mbouyer/marine_chartplotter/software/edisplay/pic/usb.c

// Firmware framework for USB I/O on PIC 18F2455 (and siblings)
// Copyright (C) 2005 Alexander Enzmann
//
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
// Modifications for SDCC2.8.0 and for loading under UBW Bootloader

#include <pic18fregs.h>
#include <string.h>
#include <stdio.h>
#include "usb.h"
#include "version.h"

#define ALLOW_SUSPEND 0

// DBUG_LEVL bitmasks to turn on/off verbosity 
// Excessive debug use may cause USB Congestion .. YMMV 
#define DBUG_CALL 9
#define DBUG_PTXN 8
#define DBUG_UTXN 7
#define DBUG_UDAT 6	
#define DBUG_UCFG 5	
#define DBUG_UGEN 4	
#define DBUG_UVENDOR 3	
#define DBUG_UNU1 2	
#define DBUG_UNU0 1	
#
// DBUG_LEVL >= 0x 80:Calls 40:ProcUSBTxns 20:Data 10:Config 08:Generic 04:VENDOR
// eg For debug messages for all below "ProcessUSBTransactions()"	
//#define DBUG_LEVL 0x3F
#define DBUG_LEVL 0x00

// Device and configuration descriptors.	These are used as the
// host enumerates the device and discovers what class of device
// it is and what interfaces it supports.
#define DEVICE_DESCRIPTOR_SIZE 0x12
#define CONFIG_HEADER_SIZE	0x09
#define VENDOR_DESCRIPTOR_SIZE 0x20
#define VENDOR_HEADER_SIZE 0x09 
typedef struct _configStruct {
	byte configHeader[CONFIG_HEADER_SIZE];
	byte VENDORDescriptor[VENDOR_DESCRIPTOR_SIZE];
} ConfigStruct;

// Global variables
byte deviceState;
byte remoteWakeup;
byte deviceAddress;
byte selfPowered;
byte currentConfiguration;

// Control Transfer Stages - see USB spec chapter 5
#define SETUP_STAGE		0 // Start of a control transfer (followed by 0 or more data stages)
#define DATA_OUT_STAGE 1 // Data from host to device
#define DATA_IN_STAGE	2 // Data from device to host
#define STATUS_STAGE	 3 // Unused - if data I/O went ok, then back to Setup

byte ctrlTransferStage; // Holds the current stage in a control transfer
byte VENDORPostProcess;	// Set to 1 if VENDOR needs to process after the data stage
byte requestHandled;	// Set to 1 if request was understood and processed.

byte *outPtr;		// Data to send to the host
byte *inPtr;		// Data from the host
word wCount;		// Number of bytes of data

// VENDOR Class variables
byte VENDORIdleRate;
byte VENDORProtocol;	// [0] Boot Protocol [1] Report Protocol
byte VENDORRxLen;	// # of bytes put into buffer

const byte deviceDescriptor[] =
{
	0x12, 0x01, // bLength, bDescriptorType
	0x00, 0x02, // bcdUSB (low byte), bcdUSB (high byte)
	0xff, 0xff, // bDeviceClass, bDeviceSubClass
	0xff, E0SZ, // bDeviceProtocl, bMaxPacketSize
	0xD8, 0x04, // idVendor (low byte), idVendor (high byte)
	0x41, 0x45, // idProduct (low byte), idProduct (high byte)
	REV_MINOR, REV_MAJOR, // bcdDevice (low byte), bcdDevice (high byte)
	0x01, 0x02, // iManufacturer, iProduct
	0x00, 0x01  // iSerialNumber (none), bNumConfigurations
};

// Total config size is 0x09 + 0x09 + 0x09 + 0x07 + 0x07+ 0x07 = 0x30
#define CFSZ 0x30

const ConfigStruct configDescriptor =
{
	{
		// Configuration descriptor
		0x09, 0x02, // bLength, bDescriptorType (Configuration)
		CFSZ, 0x00, // wTotalLength (low), wTotalLength (high)
		0x01, 0x01, // bNumInterfaces, bConfigurationValue
		0x00, 0xA0, // iConfiguration, bmAttributes ()
		0x32,	 // bMaxPower
	},
	{
		// VENDOR Interface descriptor
		0x09, 0x04, // bLength, bDescriptorType (Interface)
		0x00, 0x00, // bInterfaceNumber, bAlternateSetting
		0x03, 0xff, // bNumEndpoints, bInterfaceClass (VENDOR)
		0xff, 0xff, // bInterfaceSubclass, bInterfaceProtocol,
		0x00,	 // iInterface
		// VENDOR Endpoint 1 In
		0x07, 0x05, // bLength, bDescriptorType (Endpoint)
		0x81, 0x03, // bEndpointAddress, bmAttributes (Interrupt)
		VENDOR_INPUT_INTR_BYTES, 0x00, // wMaxPacketSize (low), wMaxPacketSize (high)
		0x0a,	 // bInterval (10 millisecond)
		// VENDOR Endpoint 1 Out
		0x07, 0x05, // bLength, bDescriptorType (Endpoint)
		0x01, 0x03, // bEndpointAddress, bmAttributes (Interrupt)
		VENDOR_OUTPUT_INTR_BYTES, 0x00, // wMaxPacketSize (low), wMaxPacketSize (high)
		0x01,	 // bInterval (1 millisecond)
		// VENDOR Endpoint 2 Out
		0x07, 0x05, // bLength, bDescriptorType (Endpoint)
		0x02, 0x02, // bEndpointAddress, bmAttributes (Interrupt)
		VENDOR_OUTPUT_BULK_BYTES, 0x00, // wMaxPacketSize (low), wMaxPacketSize (high)
		0x01,	 // bInterval (1 millisecond)
	}
};

const byte stringDescriptor0[] =
{
	0x04, STRING_DESCRIPTOR,
	0x09, 0x04,
};

const byte stringDescriptor1[] =
{
	0x16, STRING_DESCRIPTOR, // bLength, bDscType
	'M', 0x00, 'B', 0x00, ' ', 0x00, 'd', 0x00,
	'e', 0x00, 'v', 0x00, 'i', 0x00, 'c', 0x00,
	'e', 0x00, 's', 0x00,
};
const byte stringDescriptor2[] =
{
	0x1a, STRING_DESCRIPTOR,
	'U', 0x00, 'S', 0x00, 'B', 0x00, ' ', 0x00,
	'e', 0x00, 'D', 0x00, 'i', 0x00, 's', 0x00,
	'p', 0x00, 'l', 0x00, 'a', 0x00, 'y', 0x00,
};

volatile BDT __at(BDT_BASE + 0x00) ep0Bo;					//Endpoint #0 BD Out
volatile BDT __at(BDT_BASE + 0x04) ep0Bi;					//Endpoint #0 BD In
volatile BDT __at(BDT_BASE + 0x08) ep1Bo;					//Endpoint #1 BD Out
volatile BDT __at(BDT_BASE + 0x0c) ep1Bi;					//Endpoint #1 BD In
volatile BDT __at(BDT_BASE + 0x10) ep2Bo;					//Endpoint #2 BD Out

// TBD: add definitions for additional endpoints (2-16).

// Put endpoint 0 buffers into dual port RAM
#pragma udata usbram4 SetupPacket controlTransferBuffer
volatile setupPacketStruct SetupPacket;
volatile byte controlTransferBuffer[E0SZ];

// Put USB I/O buffers into dual port RAM.
#pragma udata usbram5 VENDORRxBufferB0 VENDORTxIntrBuffer
#pragma udata usbram5 VENDORRxBufferB1 VENDORRxIntrBuffer

// VENDOR specific buffers
volatile byte VENDORRxBufferB0[VENDOR_OUTPUT_BULK_BYTES];
volatile byte VENDORRxBufferB1[VENDOR_OUTPUT_BULK_BYTES];
volatile byte VENDORRxIntrBuffer[VENDOR_OUTPUT_INTR_BYTES];
volatile byte VENDORTxIntrBuffer[VENDOR_INPUT_INTR_BYTES];

static unsigned char activeBulk;

//
// Start of code for VENDOR specific code.
//

// Send up to len bytes to the host. The actual number of bytes sent is returned
// to the caller. If the send failed (usually because a send was attempted while
// the SIE was busy processing the last request), then 0 is returned.
byte
VENDORTxReport(byte *buffer, byte len)
{
	byte i;
#if DBUG_LEVL >= DBUG_UCFG
	printf("VENDORTxReport: %d\r\n", (word)len);
#endif
	// If the CPU still owns the SIE, then don't try to send anything.
	if (ep1Bi.Stat & UOWN)
		return 0;
	// Truncate requests that are too large. TBD: send 
	if(len > VENDOR_INPUT_INTR_BYTES)
		len = VENDOR_INPUT_INTR_BYTES;
	 // Copy data from user's buffer to dual-ram buffer
	for (i = 0; i < len; i++)
		VENDORTxIntrBuffer[i] = buffer[i];
	// Toggle the data bit and give control to the SIE
	ep1Bi.Cnt = len;
	if(ep1Bi.Stat & DTS)
		ep1Bi.Stat = UOWN | DTSEN;
	else
		ep1Bi.Stat = UOWN | DTS | DTSEN;
	return len;
}

// Read up to len bytes from VENDOR output buffer. Actual number of bytes put
// into buffer is returned. If there are fewer than len bytes, then only the
// available bytes will be returned. Any bytes in the buffer beyond len will
// be discarded.
byte
VENDORRxReport(byte *buffer, byte len)
{
	VENDORRxLen = 0;
#if DBUG_LEVL >= DBUG_UDAT
	// printf("VENDORRxReport: %d\r\n", len);
#endif

	// If the SIE doesn't own the output buffer descriptor, then it is
	// safe to pull data from it.
	if(!(ep1Bo.Stat & UOWN)) {
		// See if the host sent fewer bytes that we asked for.
		if(len > ep1Bo.Cnt)
			len = ep1Bo.Cnt;

		// Copy data from dual-ram buffer to user's buffer
		for(VENDORRxLen = 0; VENDORRxLen < len; VENDORRxLen++) {
			buffer[VENDORRxLen] = VENDORRxIntrBuffer[VENDORRxLen];
		}
#if DBUG_LEVL >= DBUG_UDAT
		printf("VENDORRxReport: %d: 0x%hx 0x%hx 0x%hx 0x%hx\r\n",
		    (word)len, (byte)buffer[0], (byte)buffer[1],
		    (byte)buffer[2], (byte)buffer[3]);
#endif
		// Reset the VENDOR output buffer descriptor so the host
		// can send more data.
		ep1Bo.Cnt = VENDOR_OUTPUT_INTR_BYTES;
		if(ep1Bo.Stat & DTS)
			ep1Bo.Stat = UOWN | DTSEN;
		else
			ep1Bo.Stat = UOWN | DTS | DTSEN;
	}
	return VENDORRxLen;
}

// Read up to len bytes from VENDOR output buffer. Actual number of bytes
// put into buffer is returned. If there are fewer than len bytes, then
// only the available bytes will be returned. Any bytes in the buffer
// beyond len will be discarded.

short
VENDORRxBulk()
{
#if DBUG_LEVL >= DBUG_UDAT
	// printf("VENDORRxReport: %d\r\n", len);
#endif

	// If the SIE doesn't own the output buffer descriptor, then it
	// is safe to pull data from it.
	if(!(ep2Bo.Stat & UOWN)) {
		// See if the host sent fewer bytes that we asked for.
		short len = ep2Bo.Cnt;

#if DBUG_LEVL >= DBUG_UDAT
		printf("VENDORRxReport: %d: 0x%hx 0x%hx 0x%hx 0x%hx\r\n",
		   (word)len, (byte)buffer[0], (byte)buffer[1],
		   (byte)buffer[2], (byte)buffer[3]);
#endif
		// Reset the VENDOR output buffer descriptor so the host
		// can send more data.
		if (activeBulk == 0) {
			activeBulk = 1;
			ep2Bo.ADDR = PTR16(&VENDORRxBufferB1[0]);
		} else {
			len |= (short)0x100;
			activeBulk = 0;
			ep2Bo.ADDR = PTR16(&VENDORRxBufferB0[0]);
		}
		ep2Bo.Cnt = VENDOR_OUTPUT_BULK_BYTES;
		if(ep2Bo.Stat & DTS)
			ep2Bo.Stat = UOWN | DTSEN;
		else
			ep2Bo.Stat = UOWN | DTS | DTSEN;
		return len;
	}
	return 0;
}

// After configuration is complete, this routine is called to initialize
// the endpoints (e.g., assign buffer addresses).
static void
VENDORInitEndpoint(void)
{
	VENDORRxLen =0;
#if DBUG_LEVL >= DBUG_UCFG
	printf("VENDORInitEndpoint\r\n");
#endif

	// Turn on both in and out for this endpoint
	UEP1 = 0x1E;
	UEP2 = 0x1C;
	ep1Bo.Cnt = sizeof(VENDORRxIntrBuffer);
	ep1Bo.ADDR = PTR16(&VENDORRxIntrBuffer[0]);
	ep1Bo.Stat = UOWN | DTSEN;

	ep1Bi.ADDR = PTR16(&VENDORTxIntrBuffer[0]);
	ep1Bi.Stat = DTS;

	ep2Bo.Cnt = VENDOR_OUTPUT_BULK_BYTES;
	ep2Bo.ADDR = PTR16(&VENDORRxBufferB0[0]);
	ep2Bo.Stat = UOWN | DTSEN;
	activeBulk = 0;
}

// Process VENDOR specific requests
static void
ProcessVENDORRequest(void)
{
	byte bRequest;
	 // Has to be to the VENDOR interface
	if((SetupPacket.bmRequestType & 0x1F) != 0x01 || (SetupPacket.wIndex0 != 0x00))
		return;
	bRequest = SetupPacket.bRequest;
	if (bRequest == GET_DESCRIPTOR) {
		// Request for a descriptor.
		byte descriptorType	= SetupPacket.wValue1;
		if (descriptorType == VENDOR_DESCRIPTOR) {
#if DBUG_LEVL >= DBUG_UVENDOR
			printf("VENDOR: VENDOR_DESCRIPTOR\r\n");
#endif
			// VENDOR descriptor.
			requestHandled = 1;
			//typecast below got it working with SDCC 2.8.0 
			outPtr = (unsigned char *) (&configDescriptor.VENDORDescriptor);
			wCount = VENDOR_HEADER_SIZE;
		}
		else if (descriptorType == PHYSICAL_DESCRIPTOR) {
#if DBUG_LEVL >= DBUG_UVENDOR
			printf("VENDOR: PHYSICAL_DESCRIPTOR\r\n");
#endif
		}
		else {
#if DBUG_LEVL >= DBUG_UVENDOR
			printf("VENDOR: Unsupported descriptor: 0x%x\r\n",
			    SetupPacket.wValue1);
#endif
		}
	}
	if ((SetupPacket.bmRequestType & 0x60) != 0x20) {
#if DBUG_LEVL >= DBUG_UVENDOR
		printf("Not CLASS request: 0x%x, 0x%x\r\n",
		    (word)(SetupPacket.bmRequestType & 0x60),
		    (word)SetupPacket.bRequest);
#endif
		return;
	}
	if (bRequest == GET_IDLE) {
#if DBUG_LEVL >= DBUG_UVENDOR
		printf("VENDOR: GET_IDLE\r\n");
#endif
		requestHandled = 1;
		outPtr = &VENDORIdleRate;
		wCount = 1;
	}
	else if (bRequest == SET_IDLE) {
#if DBUG_LEVL >= DBUG_UVENDOR
		printf("VENDOR: SET_IDLE\r\n");
#endif
		requestHandled = 1;
		VENDORIdleRate = SetupPacket.wValue1;
	}
	else if (bRequest == GET_PROTOCOL) {
#if DBUG_LEVL >= DBUG_UVENDOR
		printf("VENDOR: GET_PROTOCOL\r\n");
#endif
		requestHandled = 1;
		outPtr = &VENDORProtocol;
		wCount = 1;
	}
	else if (bRequest == SET_PROTOCOL) {
#if DBUG_LEVL >= DBUG_UVENDOR
		printf("VENDOR: SET_PROTOCOL\r\n");
#endif
		requestHandled = 1;
		VENDORProtocol = SetupPacket.wValue0;
	}
	else {
#if DBUG_LEVL >= DBUG_UVENDOR
		printf("VENDOR: Unknown request: 0x%x\r\n", SetupPacket.bRequest);
#endif
	}
}

//
// Start of code to process standard requests (USB chapter 9)
//

// Process GET_DESCRIPTOR
static void
GetDescriptor(void)
{
#if DBUG_LEVL >= DBUG_UCFG
	printf("GetDescriptor() ntry\r\n");
	printf("  @ntry StupPckt.RequType:x%hx .Value0:x%hx .Value1:x%hx\r\n",
	    SetupPacket.bmRequestType, SetupPacket.wValue0,
	    SetupPacket.wValue1);
#endif
	if(SetupPacket.bmRequestType == 0x80) {
		byte descriptorType  = SetupPacket.wValue1;
		byte descriptorIndex = SetupPacket.wValue0;

		if (descriptorType == DEVICE_DESCRIPTOR) {
			requestHandled = 1;
			outPtr = (byte *)&deviceDescriptor;
			//typecast below got it working with SDCC 2.8.0 
			wCount = (word)(DEVICE_DESCRIPTOR_SIZE);
#if DBUG_LEVL > DBUG_UCFG
			printf("Resp DVCE_DSCR OPtr:x%X wLen:d%d\r\n",
			    outPtr, wCount);
#endif
		}
		else if (descriptorType == CONFIGURATION_DESCRIPTOR) {
#if DBUG_LEVL > DBUG_UCFG
			printf("CONFIGURATION_DESCRIPTOR: %d\r\n",
			    descriptorIndex);
#endif
			requestHandled = 1;
#if 0
			outPtr = (byte *)&configDescriptor;
			// wCount = *(outPtr + 2);
			wCount = CFSZ;
#else
			// SDCC 2.5 makes bad code with the following two lines.
			// The unusual thing is that it is the first of the
			// two lines that is compiled incorrectly (outPtr gets
			// the contents of configDescriptor rather than the
			// address), even though it
			// is the second line that changes from above.
			outPtr = (byte *)&configDescriptor;
			wCount = configDescriptor.configHeader[2]; // Note: SDCC makes bad code with this
#endif
#if DBUG_LEVL > DBUG_UCFG
			printf("Total config size: %d\r\n", wCount);
#endif
		}
		else if (descriptorType == STRING_DESCRIPTOR) {
#if DBUG_LEVL > DBUG_UCFG
			printf("STRING_DESCRIPTOR: %d\r\n",
			    (word)descriptorIndex);
#endif
			requestHandled = 1;
			if (descriptorIndex == 0)
			//typecast below got it working with SDCC 2.8.0 
				outPtr = (unsigned char *) (&stringDescriptor0);
			else if (descriptorIndex == 1)
			//typecast below got it working with SDCC 2.8.0 
				outPtr = (unsigned char *) (&stringDescriptor1);
			else
			//typecast below got it working with SDCC 2.8.0 
				outPtr = (unsigned char *) (&stringDescriptor2);
			wCount = *outPtr;
		}
		else {
#if DBUG_LEVL > DBUG_UCFG
			printf("Unknown Descriptor: 0x%ux\r\n",
			    (word)descriptorType);
#endif
		}
	}
}

// Process GET_STATUS
static void
GetStatus(void)
{
	 // Mask off the Recipient bits
	 byte recipient = SetupPacket.bmRequestType & 0x1F;
#if DBUG_LEVL >= DBUG_UGEN
	 printf("GetStatus\r\n");
#endif
	 controlTransferBuffer[0] = 0;
	 controlTransferBuffer[1] = 0;
	 // See where the request goes
	 if (recipient == 0x00) {
		 // Device
		 requestHandled = 1;
		 // Set bits for self powered device and remote wakeup.
		 if (selfPowered)
			 controlTransferBuffer[0] |= 0x01;
		 if (remoteWakeup)
			 controlTransferBuffer[0] |= 0x02;
	 }
	 else if (recipient == 0x01) {
		 // Interface
		 requestHandled = 1;
	 }
	 else if (recipient == 0x02) {
		 // Endpoint
		 byte endpointNum = SetupPacket.wIndex0 & 0x0F;
		 byte endpointDir = SetupPacket.wIndex0 & 0x80;
		 requestHandled = 1;
		 // Endpoint descriptors are 8 bytes long, with each in and
		 // out taking 4 bytes within the endpoint. (See PIC datasheet.)
		 inPtr = (byte *)&ep0Bo + (endpointNum * 8);
		 if (endpointDir)
			 inPtr += 4;
		 if(*inPtr & BSTALL)
			 controlTransferBuffer[0] = 0x01;
	 }
	 if (requestHandled) {
		 outPtr = (byte *)&controlTransferBuffer;
		 wCount = 2;
	 }
}

// Process SET_FEATURE and CLEAR_FEATURE
static void
SetFeature(void)
{
	byte recipient = SetupPacket.bmRequestType & 0x1F;
	byte feature = SetupPacket.wValue0;
#if DBUG_LEVL >= DBUG_UCFG
	printf("SetFeature\r\n");
#endif
	if (recipient == 0x00) {
		// Device
		if (feature == DEVICE_REMOTE_WAKEUP) {
			requestHandled = 1;
			if (SetupPacket.bRequest == SET_FEATURE)
				remoteWakeup = 1;
			else
				remoteWakeup = 0;
		}
		// TBD: Handle TEST_MODE
	}
	else if (recipient == 0x02) {
		// Endpoint
		byte endpointNum = SetupPacket.wIndex0 & 0x0F;
		byte endpointDir = SetupPacket.wIndex0 & 0x80;
		if ((feature == ENDPOINT_HALT) && (endpointNum != 0)) {
			// Halt endpoint (as long as it isn't endpoint 0)
			requestHandled = 1;
			// Endpoint descriptors are 8 bytes long, with each
			// in and out taking 4 bytes within the endpoint.
			// (See PIC datasheet.)
			inPtr = (byte *)&ep0Bo + (endpointNum * 8);
			if (endpointDir)
				inPtr += 4;
			if(SetupPacket.bRequest == SET_FEATURE)
				*inPtr = 0x84;
			else {
				if(endpointDir == 1)
					*inPtr = 0x00;
				else
					*inPtr = 0x88;
			}
		}
	}
}

static void
ProcessStandardRequest(void)
{
	byte request = SetupPacket.bRequest;

	if((SetupPacket.bmRequestType & 0x60) != 0x00)
		// Not a standard request - don't process here.	Class or Vendor
		// requests have to be handled seperately.
		return;

	if (request == SET_ADDRESS) {
		// Set the address of the device. All future requests
		// will come to that address.	Can't actually set UADDR
		// to the new address yet because the rest of the SET_ADDRESS
		// transaction uses address 0.
#if DBUG_LEVL >= DBUG_UDAT
		printf("SET_ADDRESS: %uhx\r\n", SetupPacket.wValue0);
#endif
		requestHandled = 1;
		deviceState = ADDRESS;
		deviceAddress = SetupPacket.wValue0;
	}
	else if (request == GET_DESCRIPTOR) {
		GetDescriptor();
	}
	else if (request == SET_CONFIGURATION) {
#if DBUG_LEVL >= DBUG_UDAT
		printf("SET_CONFIGURATION %d\r\n", SetupPacket.wValue0);
#endif
		requestHandled = 1;
		currentConfiguration = SetupPacket.wValue0;
		// TBD: ensure the new configuration value is one that
		// exists in the descriptor.
		if (currentConfiguration == 0)
			// If configuration value is zero, device is put in
			// address state (USB 2.0 - 9.4.7)
			deviceState = ADDRESS;
		else {
			// Set the configuration.
			deviceState = CONFIGURED;

			// Initialize the endpoints for all interfaces
			VENDORInitEndpoint();

			// TBD: Add initialization code here for any additional
			// interfaces beyond the one used for the VENDOR
		}
	}
	else if (request == GET_CONFIGURATION) {
#if DBUG_LEVL >= DBUG_UCFG
	printf("GET_CONFIGURATION\r\n");
#endif
		requestHandled = 1;
		outPtr = (byte*)&currentConfiguration;
		wCount = 1;
	}
	else if (request == GET_STATUS) {
		 GetStatus();
	}
	else if ((request == CLEAR_FEATURE) ||
	    (request == SET_FEATURE)) {
		SetFeature();
	}
	else if (request == GET_INTERFACE) {
		// No support for alternate interfaces.	Send
		// zero back to the host.
#if DBUG_LEVL >= DBUG_UCFG
		printf("GET_INTERFACE\r\n");
#endif
		requestHandled = 1;
		controlTransferBuffer[0] = 0;
		//typecast below got it working with SDCC 2.8.0 
		outPtr = (unsigned char *) (&controlTransferBuffer);
		wCount = 1;
	}
	else if (request == SET_INTERFACE) {
		// No support for alternate interfaces - just ignore.
#if DBUG_LEVL >= DBUG_UCFG
		printf("SET_INTERFACE\r\n");
#endif
		requestHandled = 1;
	}
#if DBUG_LEVL >= DBUG_UCFG
	else if (request == SET_DESCRIPTOR) {
		printf("SET_DESCRIPTOR\r\n");
	}
	else if (request == SYNCH_FRAME) {
		printf("SYNCH_FRAME\r\n");
	}
	else {
		printf("Default Std Request\r\n");
	}
#endif
}

// Data stage for a Control Transfer that sends data to the host
static void
InDataStage(void)
{
	 byte i;
	word bufferSize;
	// Determine how many bytes are going to the host
	if(wCount < E0SZ)
		bufferSize = wCount;
	else
		bufferSize = E0SZ;

#if DBUG_LEVL >= DBUG_UCFG
	printf("InDataStage()\r\n");
#endif
	// Load the high two bits of the byte count into BC8:BC9
	ep0Bi.Stat &= ~(BC8 | BC9); // Clear BC8 and BC9
	ep0Bi.Stat |= (byte)((bufferSize & 0x0300) >> 8);
	ep0Bi.Cnt = (byte)(bufferSize & 0xFF);
	ep0Bi.ADDR = PTR16(&controlTransferBuffer);
	// Update the number of bytes that still need to be sent.	Getting
	// all the data back to the host can take multiple transactions, so
	// we need to track how far along we are.
	wCount = wCount - bufferSize;
	// Move data to the USB output buffer from wherever it sits now.
	inPtr = (byte *)&controlTransferBuffer;

	for (i=0;i<bufferSize;i++) {
		*inPtr++ = *outPtr++;
	}
}

// Data stage for a Control Transfer that reads data from the host
static void
OutDataStage(void)
{
	word i, bufferSize;
	bufferSize = ((0x03 & ep0Bo.Stat) << 8) | ep0Bo.Cnt;

#if DBUG_LEVL >= DBUG_UCFG
	printf("OutDataStage: %d\r\n", bufferSize);
#endif
	// Accumulate total number of bytes read
	wCount = wCount + bufferSize;
	outPtr = (byte*)&controlTransferBuffer;
	for (i=0;i<bufferSize;i++) {
#if DBUG_LEVL >= DBUG_UCFG
		printf("0x%x = 0x%x (0x%uhx) ", PTR16(inPtr), PTR16(outPtr), *outPtr);
#endif
		*inPtr++ = *outPtr++;
	}
}

// Process the Setup stage of a control transfer. This code initializes the
// flags that let the firmware know what to do during subsequent stages of
// the transfer.
static void
SetupStage(void)
{
	 // Note: Microchip says to turn off the UOWN bit on the IN direction as
	 // soon as possible after detecting that a SETUP has been received.
	 ep0Bi.Stat &= ~UOWN;
	 ep0Bo.Stat &= ~UOWN;

	 // Initialize the transfer process
	 ctrlTransferStage = SETUP_STAGE;
	 requestHandled = 0; // Default is that request hasn't been handled
	 VENDORPostProcess = 0; // Assume standard request until know otherwise
	 wCount = 0;		// No bytes transferred
	 // See if this is a standard (as definded in USB chapter 9) request
	 ProcessStandardRequest();
	 // See if the VENDOR class can do something with it.
	 if (!requestHandled)
		ProcessVENDORRequest();
	 // TBD: Add handlers for any other classes/interfaces in the device
	 if (!requestHandled) {
		 // If this service wasn't handled then stall endpoint 0
		 ep0Bo.Cnt = E0SZ;
		 ep0Bo.ADDR = PTR16(&SetupPacket);
		 ep0Bo.Stat = UOWN | BSTALL;
		 ep0Bi.Stat = UOWN | BSTALL;
	 }
	 else if (SetupPacket.bmRequestType & 0x80) {
		 // Device-to-host
		 if(SetupPacket.wLength < wCount)
			wCount = SetupPacket.wLength;
		 InDataStage();
		 ctrlTransferStage = DATA_IN_STAGE;
		 // Reset the out buffer descriptor for endpoint 0
		 ep0Bo.Cnt = E0SZ;
		 ep0Bo.ADDR = PTR16(&SetupPacket);
		 ep0Bo.Stat = UOWN;
		 // Set the in buffer descriptor on endpoint 0 to send data
		 ep0Bi.ADDR = PTR16(&controlTransferBuffer);
		 // Give to SIE, DATA1 packet, enable data toggle checks
		 ep0Bi.Stat = UOWN | DTS | DTSEN; 
	 }
	 else {
		 // Host-to-device
		 ctrlTransferStage = DATA_OUT_STAGE;
		 // Clear the input buffer descriptor
		 ep0Bi.Cnt = 0;
		 ep0Bi.Stat = UOWN | DTS | DTSEN;
		 // Set the out buffer descriptor on endpoint 0 to receive data
		 ep0Bo.Cnt = E0SZ;
		 ep0Bo.ADDR = PTR16(&controlTransferBuffer);
		 // Give to SIE, DATA1 packet, enable data toggle checks
		 ep0Bo.Stat = UOWN | DTS | DTSEN;
	 }
	 // Enable SIE token and packet processing
	 UCONbits.PKTDIS = 0;
}

// Configures the buffer descriptor for endpoint 0 so that it is waiting for
// the status stage of a control transfer.
static void
WaitForSetupStage(void)
{
	ctrlTransferStage = SETUP_STAGE;
	ep0Bo.Cnt = E0SZ;
	ep0Bo.ADDR = PTR16(&SetupPacket);
	ep0Bo.Stat = UOWN | DTSEN; // Give to SIE, enable data toggle checks
	ep0Bi.Stat = 0x00;				 // Give control to CPU
}

// This is the starting point for processing a Control Transfer. The code
// directly follows the sequence of transactions described in the USB spec
// chapter 5. The only Control Pipe in this firmware is the Default Control
// Pipe (endpoint 0).
// Control messages that have a different destination will be discarded.
static void
ProcessControlTransfer(void)
{	 
#if DBUG_LEVL >= DBUG_UCFG
	printf("ProcessControlTransfer\r\n");
#endif
	if (USTAT == 0) {
		// Endpoint 0:out
		byte PID = (ep0Bo.Stat & 0x3C) >> 2; // Pull PID from middle of BD0STAT
		if (PID == 0x0D) {
			// SETUP PID - a transaction is starting
			SetupStage();
		}		
		else if (ctrlTransferStage == DATA_OUT_STAGE) {
			// Complete the data stage so that all information has
			// passed from host to device before servicing it.
			OutDataStage();
			// Turn control over to the SIE and toggle the data bit
			if(ep0Bo.Stat & DTS)
				ep0Bo.Stat = UOWN | DTSEN;
			else
				ep0Bo.Stat = UOWN | DTS | DTSEN;
		}
		else {
			// Prepare for the Setup stage of a control transfer
			WaitForSetupStage();
		}
	}
	else if(USTAT == 0x04) {
		// Endpoint 0:in
		if ((UADDR == 0) && (deviceState == ADDRESS)) {
			// TBD: ensure that the new address matches the value of
			// "deviceAddress" (which came in through a SET_ADDRESS).
			UADDR = SetupPacket.wValue0;
#if DBUG_LEVL >= DBUG_UCFG
			printf("UADDR = 0x%x\r\n", (word)UADDR);
#endif
			if(UADDR == 0) {
				// If we get a reset after a SET_ADDRESS,
				// then we need to drop back to the Default
				// state.
				deviceState = DEFAULT;
			}	
		}
		if (ctrlTransferStage == DATA_IN_STAGE) {
			// Start (or continue) transmitting data
			InDataStage();
			// Turn control over to the SIE and toggle the data bit
			if(ep0Bi.Stat & DTS)
				ep0Bi.Stat = UOWN | DTSEN;
			else
				ep0Bi.Stat = UOWN | DTS | DTSEN;
		}
		else {
			// Prepare for the Setup stage of a control transfer
			WaitForSetupStage();
		}
	}
	else {
#if DBUG_LEVL >= DBUG_UCFG
		printf("USTAT = 0x%uhx\r\n", USTAT);
#endif
	}
}

void
EnableUSBModule(void)
{
	if(UCONbits.USBEN == 0)
	{
		UCON = 0;
		UIE = 0;
		UCONbits.USBEN = 1;
		deviceState = ATTACHED;
#if DBUG_LEVL >= DBUG_UTXN
		printf("EnabUSBM() DvState DETA <= ATTA UCON.Enab <= 1 UCON:x%hx \r\n", (byte)UCON);
#endif
	}
	else { 
#if DBUG_LEVL >= DBUG_CALL
		printf("EnabUSBM() DvState == DETA UCON Ardy Enab == 1 UCON:x%hx \r\n", (byte)UCON);
#endif
	}
	// If we are attached and no single-ended zero is detected, then
	// we can move to the Powered state.
	if ((deviceState == ATTACHED) && !UCONbits.SE0)
	{
		UIR = 0;
		UIE = 0;
		UIEbits.URSTIE = 1;
		UIEbits.IDLEIE = 1;
		deviceState = POWERED;
#if DBUG_LEVL >= DBUG_PTXN
		printf("EnabUSBM() UCON.SE0 != 1 DvState <= PWRD, UCON:x%hx \r\n", (byte)UCON);	
#endif
	}
}

// Unsuspend the device
static void
UnSuspend(void)
{
#if DBUG_LEVL >= DBUG_PTXN
	printf("UnSuspend()\r\n");
#endif
	UCONbits.SUSPND = 0;
	UIEbits.ACTVIE = 0;
	UIRbits.ACTVIF = 0;
}

// Full speed devices get a Start Of Frame (SOF) packet every 1 millisecond.
// Nothing is currently done with this interrupt (it is simply masked out).
static void
StartOfFrame(void)
{
		// TBD: Add a callback routine to do something
		UIRbits.SOFIF = 0;
}

// This routine is called in response to the code stalling an endpoint.
void
Stall(void)
{
#if DBUG_LEVL >= DBUG_PTXN
	printf("Stall\r\n");
#endif
	if(UEP0bits.EPSTALL == 1) {
		// Prepare for the Setup stage of a control transfer
		WaitForSetupStage();
		UEP0bits.EPSTALL = 0;
	}
	UIRbits.STALLIF = 0;
}

// Suspend all processing until we detect activity on the USB bus
static void
Suspend(void)
{
#if ALLOW_SUSPEND
#if DBUG_LEVL >= DBUG_PTXN
	printf("Suspend\r\n");
#endif
	UIEbits.ACTVIE = 1;
	UIRbits.IDLEIF = 0;
	UCONbits.SUSPND = 1;

	PIR2bits.USBIF = 0;
	//INTCONbits.RBIF = 0;
	PIE2bits.USBIE = 1;
	//INTCONbits.RBIE = 1;

#if 0
	// disable the USART
	RCSTAbits.CREN = 0;
	TXSTAbits.TXEN = 0;

	Sleep();
#endif

	// enable the USART
	RCSTAbits.CREN = 1;
	TXSTAbits.TXEN = 1;

	PIE2bits.USBIE = 0;
	//INTCONbits.RBIE = 0;
#endif
}

static void
BusReset()
{
	UEIR	= 0x00;
	UIR	= 0x00;
	UEIE	= 0x9f;
	UIE	= 0x7b;
	UADDR = 0x00;

	// Set endpoint 0 as a control pipe
	UEP0 = 0x16;

	// Flush any pending transactions
	while (UIRbits.TRNIF == 1)
		UIRbits.TRNIF = 0;

	// Enable packet processing
	UCONbits.PKTDIS = 0;

	// Prepare for the Setup stage of a control transfer
	WaitForSetupStage();

	remoteWakeup = 0; // Remote wakeup is off by default
	selfPowered = 0; // Self powered is off by default
	currentConfiguration = 0; // Clear active configuration
	deviceState = DEFAULT;
}

// Main entry point for USB tasks.
// Checks interrupts, then checks for transactions.
void
ProcessUSBTransactions(void)
{	 
#if DBUG_LEVL >= DBUG_CALL
	printf("ProcUSBTxcts() ntry, DevState:x%hx UCON:x%hx UIR:x%hx\r\n", deviceState, UCON, UIR);
#endif 
	// See if the device is connected yet.
	if(deviceState == DETACHED) {
#if DBUG_LEVL >= DBUG_PTXN
		printf("ProcUSBTxcts() DvStat == DETACHED exit\r\n");
#endif
		return;
	 }
	// If the USB became active then wake up from suspend
	if(UIRbits.ACTVIF && UIEbits.ACTVIE) {
#if DBUG_LEVL >= DBUG_PTXN
		printf("ProcUSBTxcts() UIR:x%hx ACTIF && ACTIE; UNSUSP() \r\n", UIR);
#endif
		UnSuspend();
	}	
	// If we are supposed to be suspended, then don't try performing any
	// processing.
	if(UCONbits.SUSPND == 1) {
#if DBUG_LEVL >= DBUG_PTXN
		printf("ProcUSBTxcts() UCON:x%hx SUSPND ==1; exit\r\n", UCON);
#endif
		return;
	}
	// Process a bus reset
	if (UIRbits.URSTIF && UIEbits.URSTIE) {
#if DBUG_LEVL >= DBUG_PTXN
		printf("ProcUSBTxcts() UIR:x%hx URSTIF && URSTIE; BusReset() \r\n", UIR);
#endif
		BusReset();
	}
	if (UIRbits.IDLEIF && UIEbits.IDLEIE){
		// No bus activity for a while - suspend the firmware
#if DBUG_LEVL >= DBUG_PTXN
		printf("ProcUSBTxcts() UIR:x%hx IDLEIF && IDLEIE; Suspend() \r\n", UIR);
#endif
		Suspend();
	}
	if (UIRbits.SOFIF && UIEbits.SOFIE){
#if DBUG_LEVL >= DBUG_PTXN
		printf("ProcUSBTxcts() UIR:x%hx SOFIF && SOFIE; StartOfFrame() \r\n", UIR);
#endif
		StartOfFrame();
	}
	if (UIRbits.STALLIF && UIEbits.STALLIE){
#if DBUG_LEVL >= DBUG_PTXN
		printf("ProcUSBTxcts() UIR:x%hx STALLIF && STALLIE; Stall() \r\n", UIR);
#endif
		Stall();
	}
	if (UIRbits.UERRIF && UIEbits.UERRIE){
		// TBD: See where the error came from.
#if DBUG_LEVL >= DBUG_PTXN
		printf("ProcUSBTxcts() UIR:x%hx UERRIF && UERRIE; clearErrs \r\n", UIR);
#endif
		// Clear errors
		UIRbits.UERRIF = 0;
	}
	// Unless we have been reset by the host, no need to keep processing
	if (deviceState < DEFAULT) {
#if DBUG_LEVL >= DBUG_PTXN
		printf("ProcUSBTxcts(): DvState < DFLT, exit\r\n");
#endif
		return;
	}
	// A transaction has finished.	Try default processing on endpoint 0.
	if(UIRbits.TRNIF && UIEbits.TRNIE)
	{
#if DBUG_LEVL >= DBUG_PTXN
		printf("ProcUSBTxcts() UIR:x%hx TRNIF && TRNIE; procCrlTxfr(), TRNIF <= 0 \r\n", UIR);
#endif
		ProcessControlTransfer();
		// Turn off interrupt
		UIRbits.TRNIF = 0;
	}
}
